JayJasonCC/release_LINduinoCAN/component_CAN&LIN/algorithms/radar.png

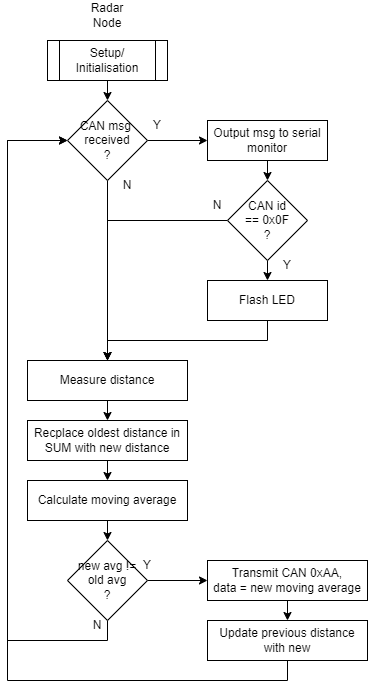
component_CAN&LIN/algorithms/radar.png
